aykutozdemir/Simple_Lab_Power_Supply/3D/banana/banana jack 4mm.png

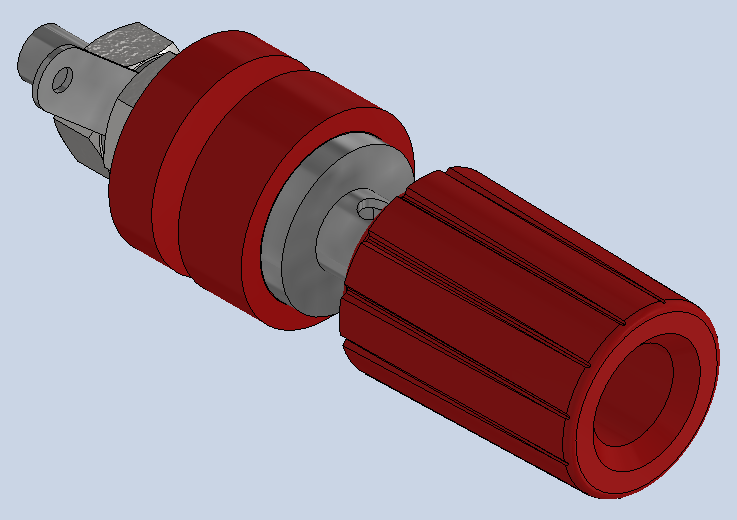
3D/banana/banana jack 4mm.png
