aykutozdemir/Simple_Lab_Power_Supply/3D/banana/preview.png

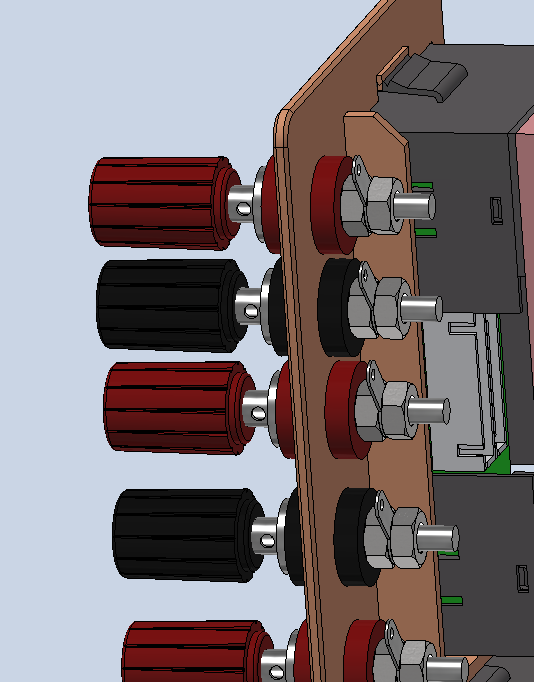
3D/banana/preview.png
