aykutozdemir/Simple_Lab_Power_Supply/3D/multimeter/V & A.JPG

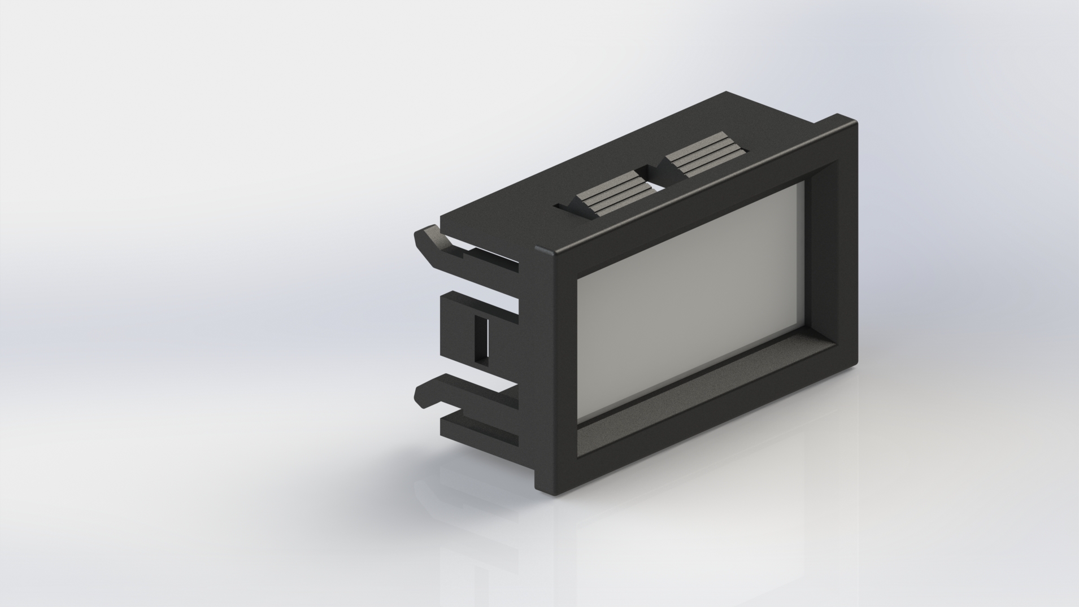
3D/multimeter/V & A.JPG
