aykutozdemir/Simple_Lab_Power_Supply/Controller/generated/3d/Controller_3d_back-right.png

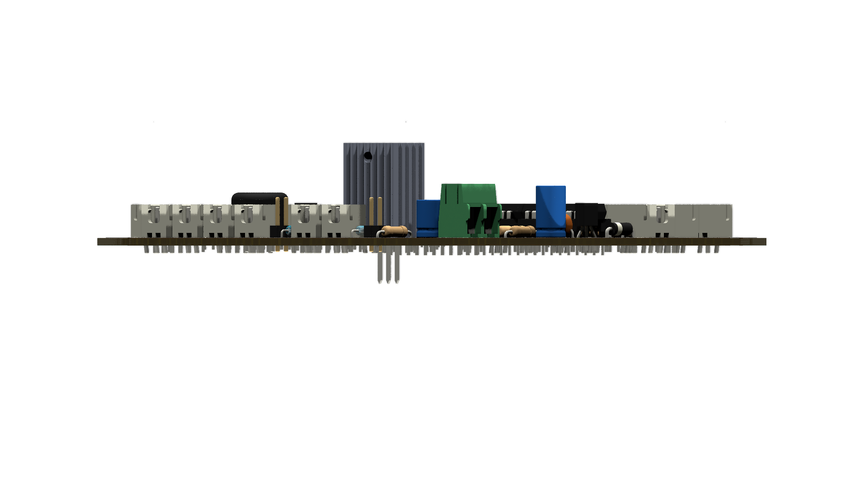
Controller/generated/3d/Controller_3d_back-right.png
