aykutozdemir/Simple_Lab_Power_Supply/Controller/generated/3d/Controller_3d_front-left-up.png

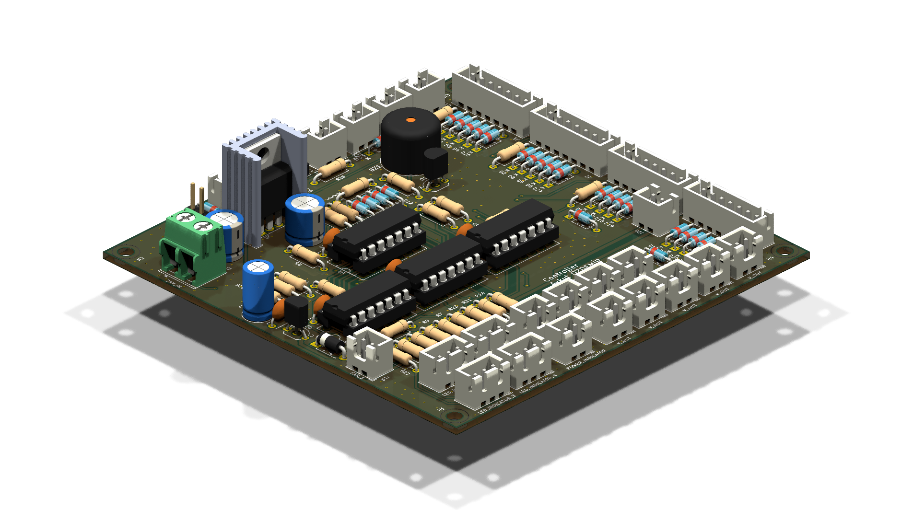
Controller/generated/3d/Controller_3d_front-left-up.png
