aykutozdemir/Simple_Lab_Power_Supply/Controller/generated/3d/Controller_3d_right.png

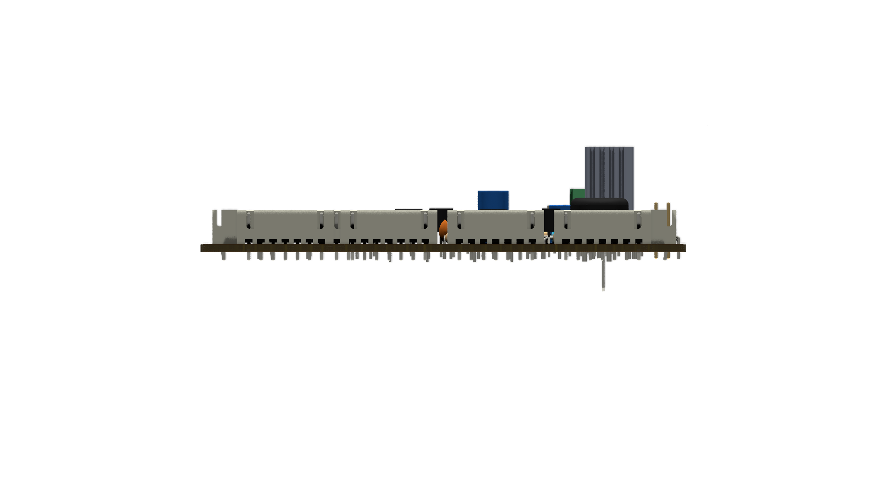
Controller/generated/3d/Controller_3d_right.png
