aykutozdemir/Simple_Lab_Power_Supply/Protection/generated/3d/Protection_3d_back-left.png

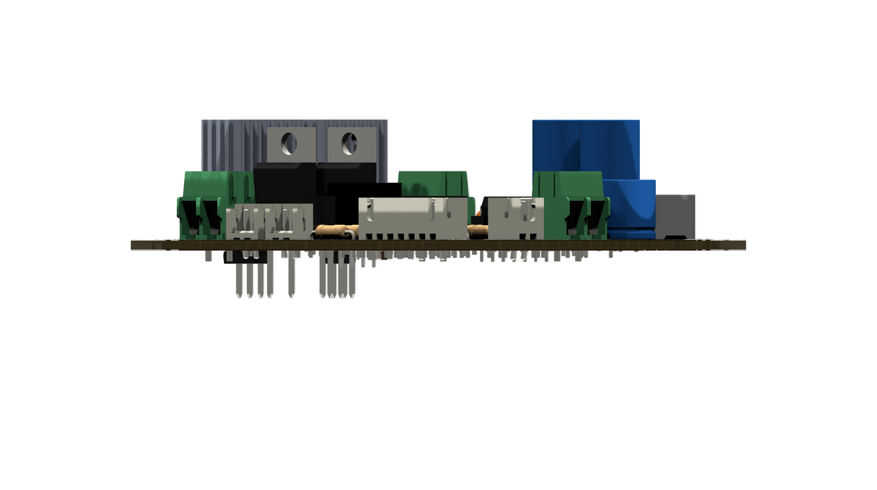
Protection/generated/3d/Protection_3d_back-left.png
