aykutozdemir/Simple_Lab_Power_Supply/Protection/generated/3d/Protection_3d_left.png

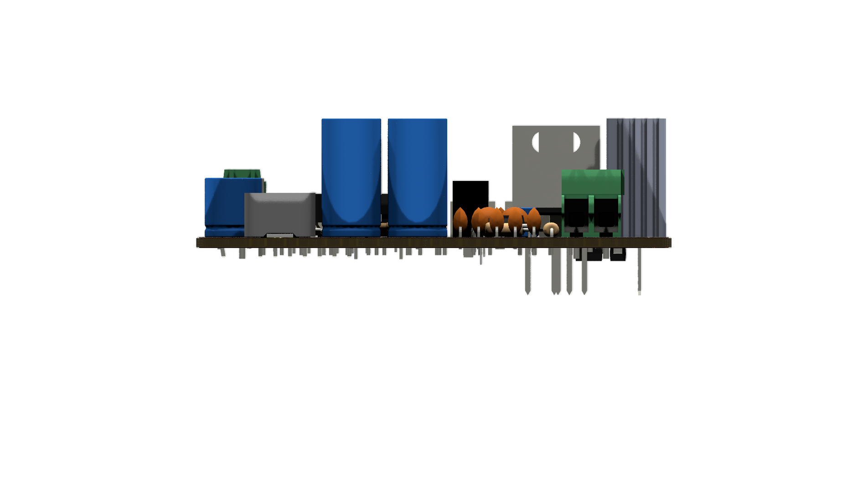
Protection/generated/3d/Protection_3d_left.png
