aykutozdemir/Simple_Lab_Power_Supply/Protection/generated/3d/Protection_3d_top-right.png

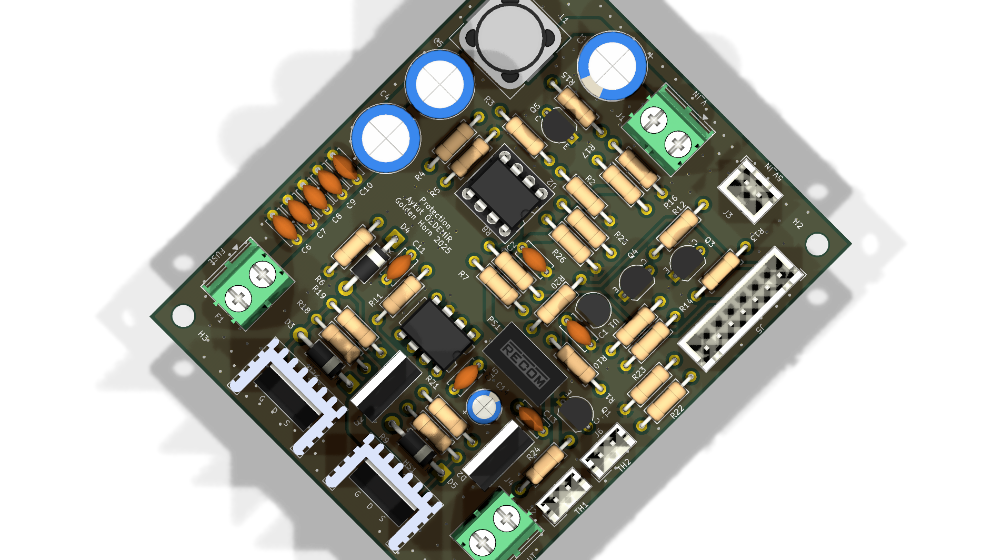
Protection/generated/3d/Protection_3d_top-right.png
