aykutozdemir/Simple_Lab_Power_Supply/3D/switch/Tekli-Montaj_Shrinkwrap_1.stl

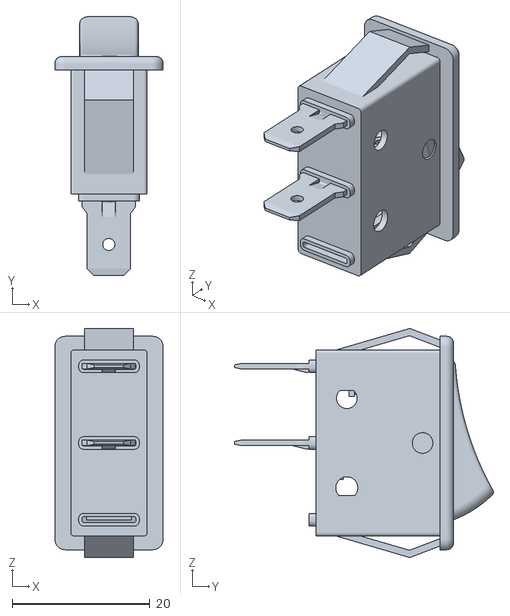
[picture p55: CAD file, 2025-09-07]
3D/switch/Tekli-Montaj_Shrinkwrap_1.stl
15.7 x 37.6 x 33.3
