aykutozdemir/Simple_Lab_Power_Supply/3D/usb/Dual USB A charger fini v004.stl

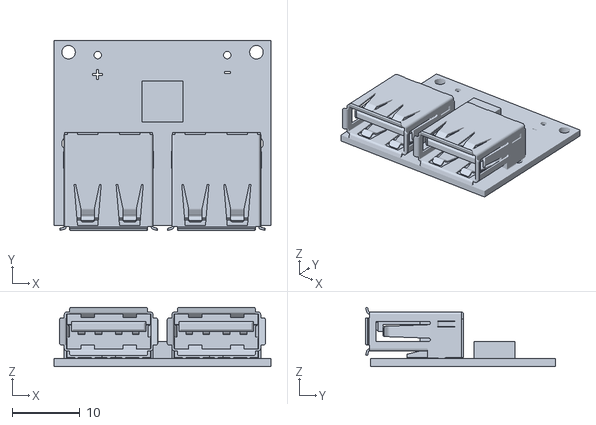
[picture p56: CAD file, 2025-09-07]
3D/usb/Dual USB A charger fini v004.stl
32.0 x 28.0 x 8.76
