aykutozdemir/Simple_Lab_Power_Supply/Protection/generated/3d/Protection_board.step

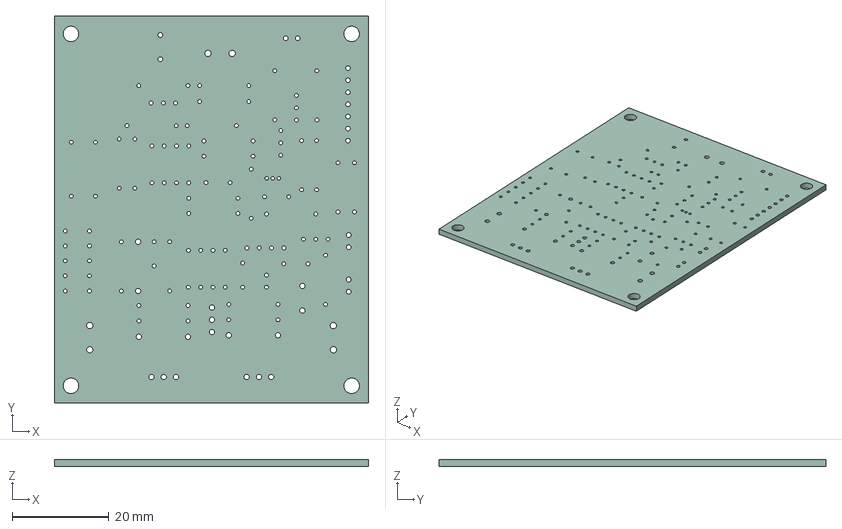
[picture p57: CAD file, 2025-09-07]
Protection/generated/3d/Protection_board.step
65.0 x 80.0 x 1.51 mm
