aykutozdemir/Simple_Lab_Power_Supply/3D/exports/mid.stl

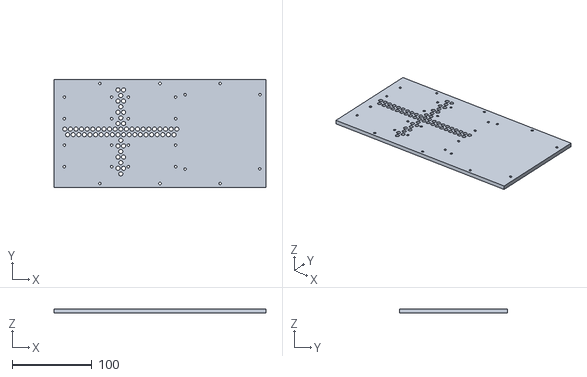
[picture p58: CAD file, 2025-09-07]
3D/exports/mid.stl
265.0 x 135.0 x 5.00
