aykutozdemir/Simple_Lab_Power_Supply/3D/pot/Knob.step

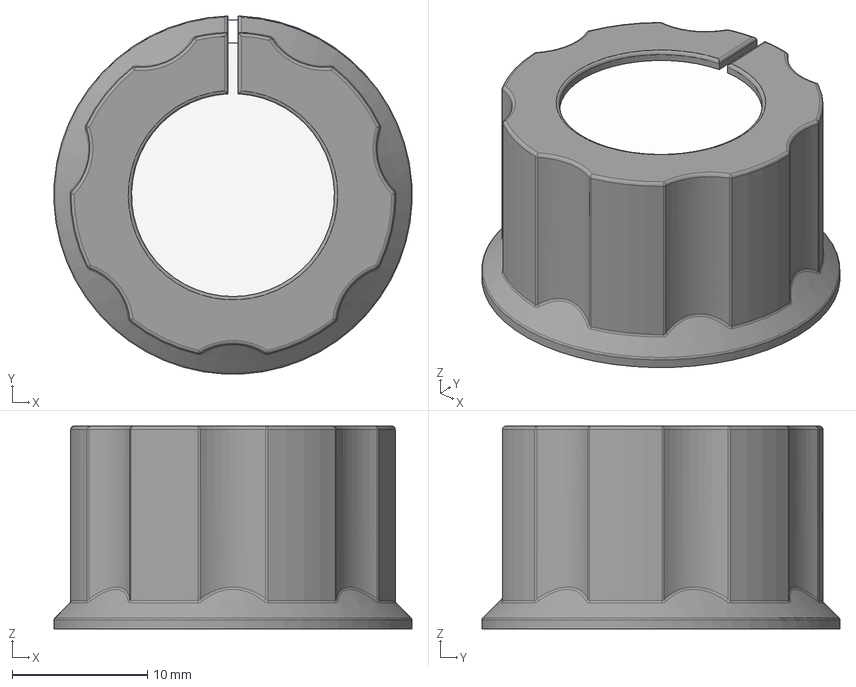
[picture p59: CAD file, 2025-09-07]
3D/pot/Knob.step
26.5 x 26.5 x 15.0 mm
