aykutozdemir/Simple_Lab_Power_Supply/3D/socket/Soket.STEP

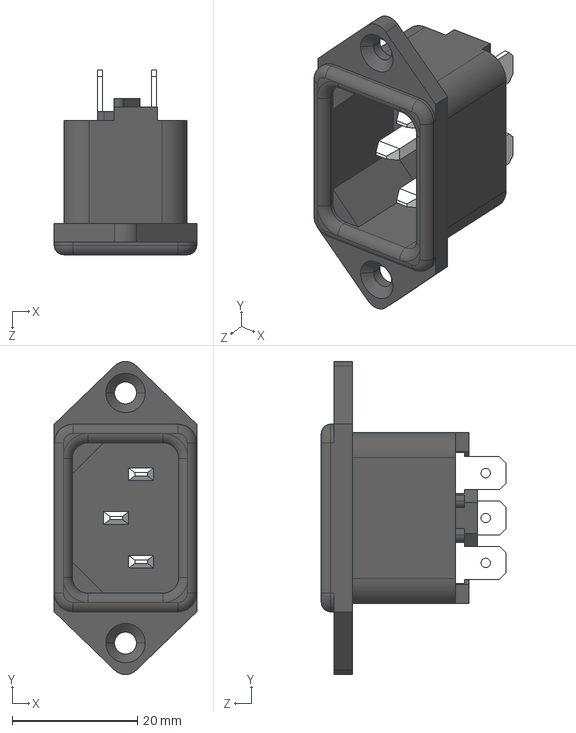
[picture p60: CAD file, 2025-09-07]
3D/socket/Soket.STEP
22.8 x 50.0 x 29.5 mm
