aykutozdemir/Simple_Lab_Power_Supply/3D/switch/SPDT_Toggle_Switch.stl

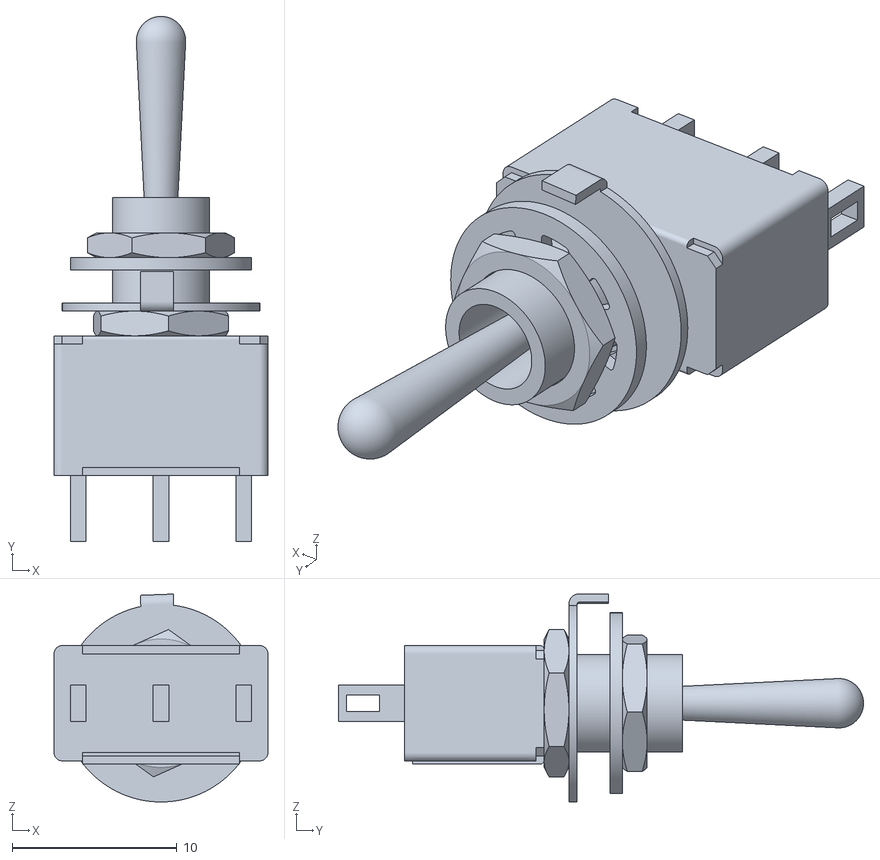
[picture p61: CAD file, 2025-09-07]
3D/switch/SPDT_Toggle_Switch.stl
13.0 x 31.9 x 12.6
