aykutozdemir/Simple_Lab_Power_Supply/3D/exports/top.stl

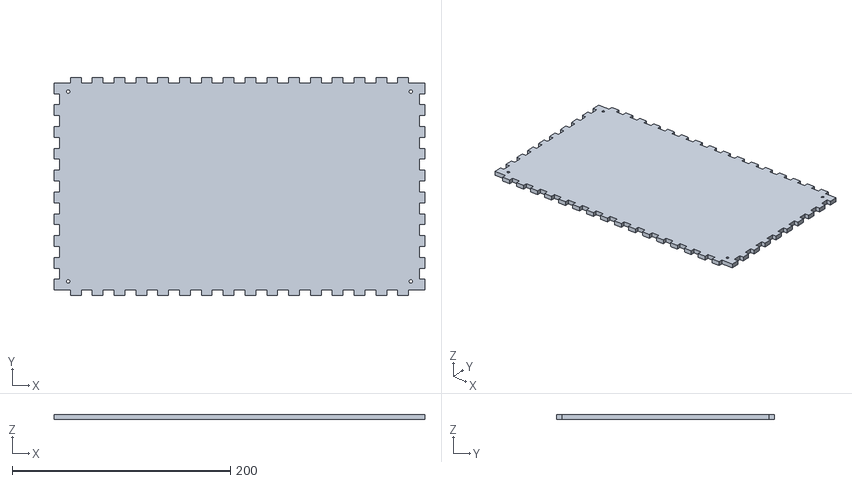
[picture p62: CAD file, 2025-09-07]
3D/exports/top.stl
340.0 x 200.0 x 5.00
