aykutozdemir/Simple_Lab_Power_Supply/3D/exports/front.stl

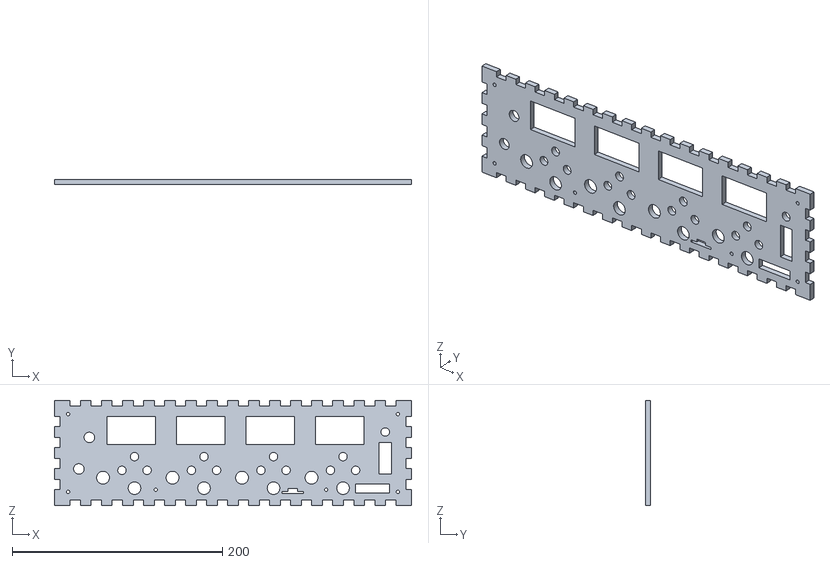
[picture p63: CAD file, 2025-09-07]
3D/exports/front.stl
340.0 x 5.00 x 100.0
