aykutozdemir/Simple_Lab_Power_Supply/3D/exports/back.stl

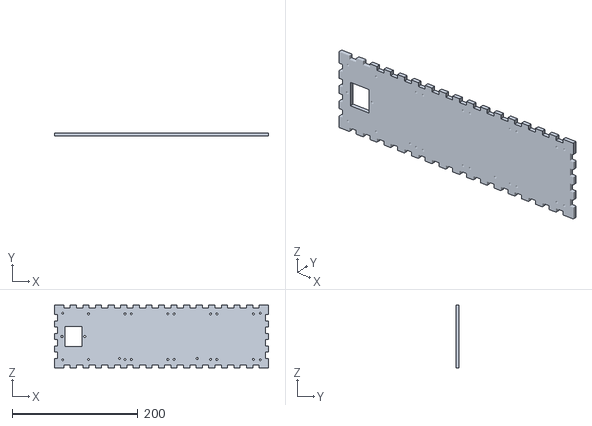
[picture p64: CAD file, 2025-09-07]
3D/exports/back.stl
340.0 x 5.00 x 100.0
