aykutozdemir/Simple_Lab_Power_Supply/3D/tri_corner/corner bracket v1.scad

// CSG file generated from FreeCAD 1.0.2
group() {
 group(){
// x-y plane triangle
difference() {
    linear_extrude(height=3) polygon(points=[[0,0],[20,0],[0,20]]);
    translate([8,8,-1]) cylinder(h=5, d=3);
}

// y-z plane triangle (rotated 90 degrees around x-axis)
difference() {
    translate([0,3,0]) rotate([90,0,0]) linear_extrude(height=3) polygon(points=[[0,0],[20,0],[0,20]]);
    translate([8,3,8]) rotate([90,0,0]) cylinder(h=5, d=3);
}

// x-z plane triangle (rotated 90 degrees around y-axis)
difference() {
    translate([3,0,0]) rotate([0,-90,0]) linear_extrude(height=3) polygon(points=[[0,0],[20,0],[0,20]]);
    translate([3,8,8]) rotate([0,-90,0]) cylinder(h=5, d=3);
}
 }
}
