aykutozdemir/Simple_Lab_Power_Supply/Controller/generated/pdf/pcb/Controller_F.Cu.pdf

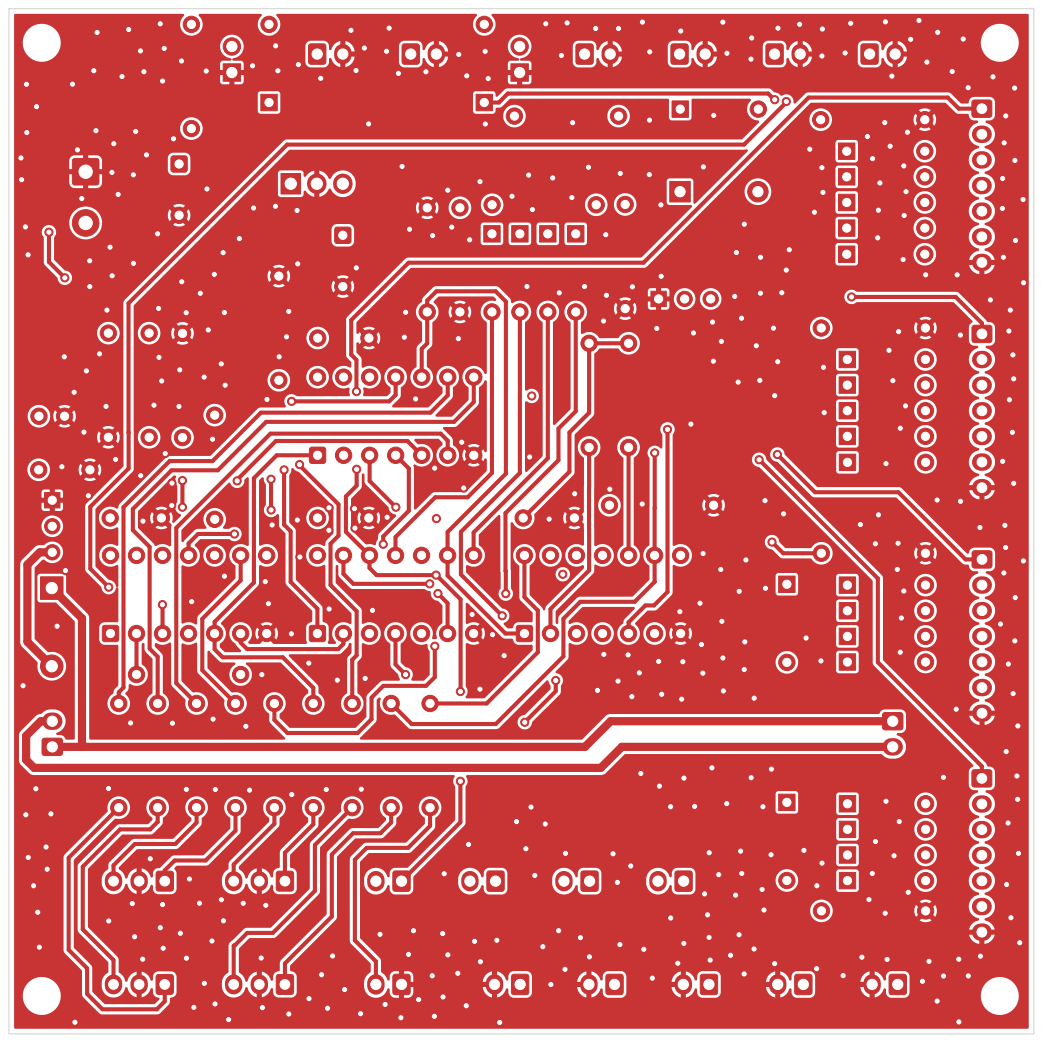
[picture p93: page 1]
