aykutozdemir/Simple_Lab_Power_Supply/Controller/generated/pdf/pcb/Controller_F.SilkS.pdf

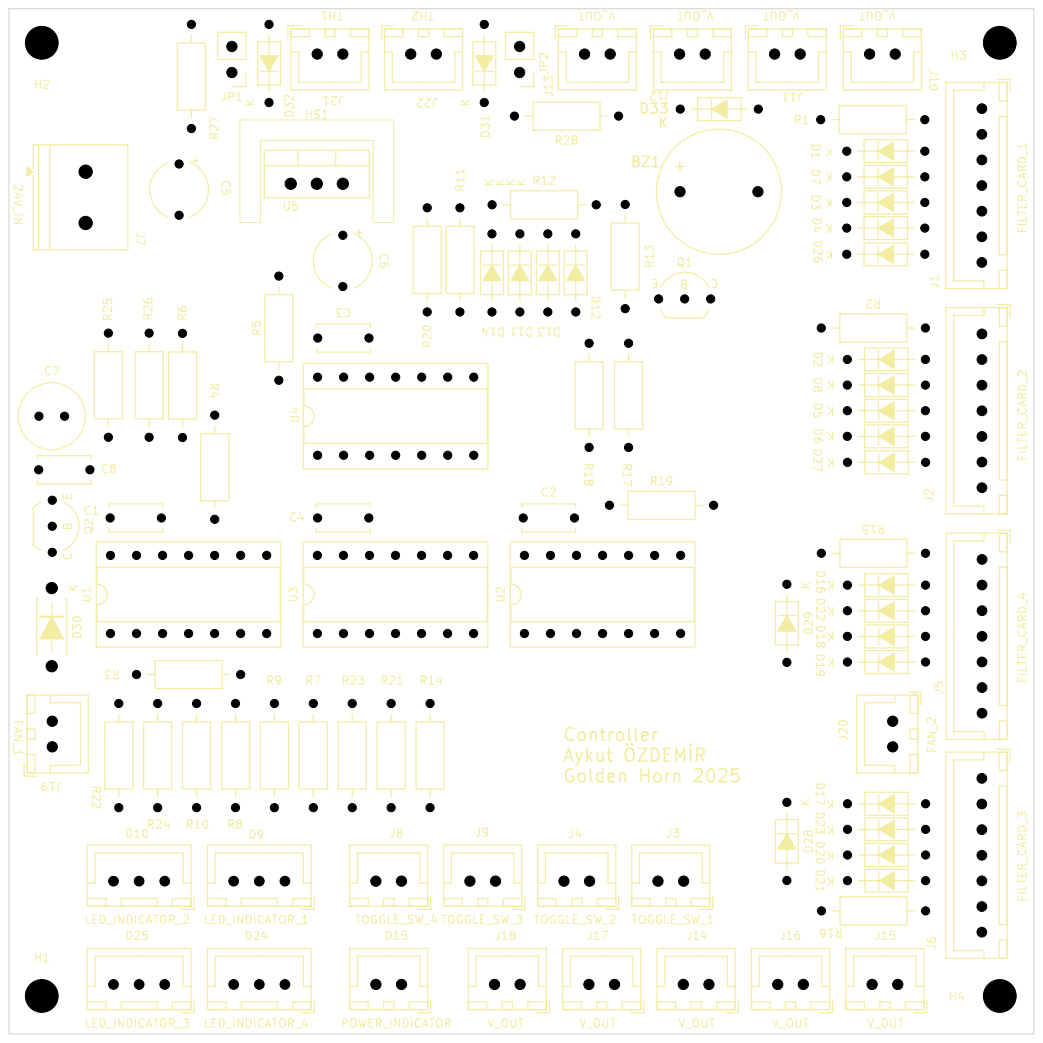
[picture p94: page 1]

Controller Aykut þÿÖZDEM0R Golden Horn 2025
